wp4032/cs107e-final-project/math.c

#include "math.h"
#include "assert.h"
#include "printf.h"

void math_init(void) {
    return;
}

// Constant values of PI π
const float _pi = 3.141592653589793;
const float _pi_2 = 1.5707963267948966;
const float _pi_4 = 0.7853981633974483;

// Table of cos
// Domain is 0 degrees to 360 degrees
static float _cos[360] = {
    1.0,
    0.9998476951563913,
    0.9993908270190958,
    0.9986295347545738,
    0.9975640502598242,
    0.9961946980917455,
    0.9945218953682733,
    0.992546151641322,
    0.9902680687415704,
    0.9876883405951378,
    0.984807753012208,
    0.981627183447664,
    0.9781476007338057,
    0.9743700647852352,
    0.9702957262759965,
    0.9659258262890683,
    0.9612616959383189,
    0.9563047559630354,
    0.9510565162951535,
    0.9455185755993168,
    0.9396926207859084,
    0.9335804264972017,
    0.9271838545667874,
    0.9205048534524404,
    0.9135454576426009,
    0.9063077870366499,
    0.898794046299167,
    0.8910065241883679,
    0.882947592858927,
    0.8746197071393957,
    0.8660254037844387,
    0.8571673007021123,
    0.848048096156426,
    0.838670567945424,
    0.8290375725550416,
    0.8191520442889918,
    0.8090169943749475,
    0.7986355100472928,
    0.788010753606722,
    0.7771459614569709,
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
};

// Table of sin
// Domain is 0 degrees to 360 degrees
static float _sin[360] = {
    0.0,
    0.01745240643728351,
    0.03489949670250097,
    0.05233595624294383,
    0.0697564737441253,
    0.08715574274765817,
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

// FUNCTION: __cos
// PARAMS: int x
// RETURNS: cos(x) where x is the integer value of the degree
float __cos(int x) {
    return _cos[x % 360];
}

// FUNCTION: __cos
// PARAMS: int x
// RETURNS: sin(x) where x is the integer value of the degree
float __sin(int x) {
    return _sin[x % 360];
}

// FUNCTION: acos
// PARAMS: int x
// RETURNS: acos(x) where x 
float __acos(int x) {
    if (x < -100 || x > 100) {
        printf("acos(x = %d) is out of the domain of acos()", x);
        assert(0);
        return 0.0;
    }
    return _acos[x + 100];
}

// FUNCTION: asin
// PARAMS: int x
// RETURNS: sin(x) where x is the integer value of the degree
float __asin(int x) {
    if (x < -100 || x > 100) {
        printf("asin(x = %d) is out of the domain of sin()", x);
        assert(0);
        return 0.0;
    }
    return _asin[x + 100];
}

// FUNCTION: atan
// PARAMS: int x
// RETURNS: sin(x) where x is the integer value of the degree
float __atan(int x) {
    if (x > 1000) {
        return _pi_2;
    }
    if (x < -1000) {
        return -1 * _pi_2;
    }
    return _atan[x + 1000];
}


// TRIGONOMETRY FUNCTIONS
// Functions that can take in floats, but will be rounded and may be incorrect

float cos(float x) {
    return __cos((int) (x));
}

float sin(float x) {
    return __sin((int) (x));
}

float tan(float x) {
    return __sin((int) (x)) / __cos((int) (x));
}

float acos(float x) {
    return __acos((int) (x * 100));
}

float asin(float x) {
    return __asin((int) (x * 100));
}

float atan(float x) {
    return __atan((int) (x * 100));
}

float atan2(float y, float x) {
    return __atan((int) ((y / x) * 100));
}


// BASIC MATH FUNCTIONS
// Math functions that are very simple such as square root and power

// FUNCTION: pwr
// PARAMS: float a, signed int b
// RETURNS: a^b where a is a float and b is an integer
// CITATION: https://www.codeproject.com/Articles/570700/SquareplusRootplusalgorithmplusforplusC
float pwr(float a, signed int b) {
    float result = 1.0;
    if (b > 0) {
        for(int i = 0; i < b; i++) {
            result *= a;
        }
    }
    if (b < 0) {
        for(int i = 0; i < (0 - b); i++){
            result *= 1 / a;
        }
    }
    return result;
}

// FUNCTION: pwr10
// PARAMS: signed int b
// RETURNS: 10^b where b is an integer
// CITATION: https://www.codeproject.com/Articles/570700/SquareplusRootplusalgorithmplusforplusC
float pwr10(signed int b) {
    return pwr(10.0, b);
}

// FUNCTION: sqrt
// PARAMS: float a
// RETURNS: √ a where a is a float; returns 0 if given a negative value
// CITATION: https://www.codeproject.com/Articles/570700/SquareplusRootplusalgorithmplusforplusC
float sqrt(float a) {
    float temp = a;
    float result = 0.0;
    int max = 8;
    double j = 1.0;

    for(int i = max; i > 0; i--){
        if(temp - ((2 * result) + (j * pwr10(i))) * (j * pwr10(i)) >= 0) {
            while(temp - ((2 * result) + (j * pwr10(i)))*(j * pwr10(i)) >= 0) {
                j++;
                if(j >= 10) break;
            }
            j--;
            temp -= ((2 * result) + (j * pwr10(i)))*(j * pwr10(i));
            result += j * pwr10(i);
            j = 1.0;
        }
    }

    for (int i = 0; i >= 0 - max; i--) {
        if(temp - ((2 * result) + (j * pwr10(i))) * (j * pwr10(i)) >= 0) {
            while(temp - ((2 * result) + (j * pwr10(i)))*(j * pwr10(i)) >= 0) {
                j++;
            }
            j--;
            temp -= ((2 * result) + (j * pwr10(i))) * (j * pwr10(i));
            result += j * pwr10(i);
        }
    }

    return result;
}

// ABSTRACT / MODULUAR MATH FUNCTIONS
// Functions that deal with integers or miscellaneous 

// FUNCTION: floor
// PARAMS: float x
// RETURNS: the integer part of x
int floor(float x) {
    return (int) x;
}

// FUNCTION: round
// PARAMS: float x
// RETURNS: rounds x to the nearest integer
int round(float x) {
    return floor(x + 0.5);
}

// FUNCTION: decimals
// PARAMS: float x
// RETURNS: the decimal part of x
float decimals(float x) {
    return x - ((float) floor(x));
}

// FUNCTION: decimals_flipped
// PARAMS: float x
// RETURNS: the (1 - decimal part of x)
float decimals_flipped(float x) {
    return 1 - decimals(x);
}

// FUNCTION: swap
// PARAMS: int *a, int *b
// RETURNS: swaps the two integers
void swap(int *a, int *b) {
    int temp = *a;
    *a = *b;
    *b = temp;
}

// FUNCTION: abs
// PARAMS: signed int a
// RETURNS: the absolute value of a signed integer
unsigned int abs(signed int a) {
  if (a < 0) {
    return a * -1;
  }
  return a;
}


// VECTOR MATH
// Functions that deal with vectors
// Ended up not using but would be interested in further developing in the future

// FUNCTION: v_dot
// PARAMS: vector_t a, vector_t b
// RETURNS: vector dot product of a and b
float v_dot(vector_t a, vector_t b) {
  return (a.x * b.x) + (a.y * b.y) + (a.z + b.z);
}

// FUNCTION: v_add
// PARAMS: vector_t a, vector_t b
// RETURNS: vector addition of a and b
vector_t v_add(vector_t a, vector_t b) {
  vector_t result;
  result.x = a.x + b.x;
  result.y = a.y + b.y;
  result.z = a.z + b.z;
  return result;
}

// FUNCTION: v_sub
// PARAMS: vector_t a, vector_t b
// RETURNS: vector subtraction of a and b
vector_t v_sub(vector_t a, vector_t b) {
  vector_t result;
  result.x = a.x - b.x;
  result.y = a.y - b.y;
  result.z = a.z - b.z;
  return result;
}

// FUNCTION: v_multiply
// PARAMS: vector_t a, vector_t b
// RETURNS: vector and scalar multplication of a and b
vector_t v_multiply(vector_t a, float b) {
  vector_t result;
  result.x = a.x * b;
  result.y = a.y * b;
  result.z = a.z * b;
  return result;
}

// FUNCTION: v_multiply
// PARAMS: vector_t a, vector_t b
// RETURNS: vector and scalar division of a and b
vector_t v_divide(vector_t a, float b) {
  vector_t result;
  result.x = a.x / b;
  result.y = a.y / b;
  result.z = a.z / b;
  return result;
}
