wp4032/cs107e-final-project/title.c

#include "gl.h"
#include "settings.h"
#include "strings.h"
#include "timer.h"
#include "armtimer.h"

#define SPACING 5

typedef struct  {
    int img_width, img_height;
    unsigned int title_img[];
} title_image_t;

static const title_image_t title;


// FUNCTION: draw_title
// PARAMS: void
// RETURNS: draws the title screen for 5 seconds
void draw_title(void) {
  armtimer_disable_interrupts();
  int x_half = SCREEN_X / 2;
  int y_half = SCREEN_Y / 2;

  // Draws image of DREAMS DON'T DIE LOGO on screen
  for(int x = 0; x < title.img_width; x++) {
    for(int y = 0; y < title.img_height; y++) {
      color_t c = (color_t) (~title.title_img[x + (y * title.img_width)]);
      if (c != 0) {
        gl_draw_pixel(x + x_half - (title.img_width / 2), y + y_half - (title.img_height / 2), c);
      }
    }
  }

  int char_width = gl_get_char_width();
  int char_height = gl_get_char_height();

  const char *welcome = "Welcome to:";
  int wel_len = strlen(welcome) * char_width;
  const char *moonwalker = "M O O N W A L K E R   V 1 . 1";
  int moon_len = strlen(moonwalker) * char_width;
  const char *credit = "Copyright William Pan (williampan@stanford.edu) 2023";
  int cred_len = strlen(credit) * char_width;
  const char *allrights = "All Rights Reserved";
  int ar_len = strlen(allrights) * char_width;

  // Draws various other text (ones above)
  gl_draw_string(x_half - (wel_len / 2), y_half - (title.img_height / 2) - char_height - SPACING, welcome, GL_WHITE);
  gl_draw_string(x_half - (moon_len / 2), y_half + (title.img_height / 2) + char_height - 10, moonwalker, GL_WHITE);
  gl_draw_string(x_half - (cred_len / 2), y_half + (title.img_height / 2) + (2 * (char_height + SPACING)) + 20, credit, GL_WHITE);
  gl_draw_string(x_half - (ar_len / 2), y_half + (title.img_height / 2) + (3 * (char_height + SPACING)) + 20, allrights, GL_WHITE);

  gl_swap_buffer();

  timer_delay(5);
  armtimer_enable_interrupts();
}


// title_image_t holds the color values of the image
static const title_image_t title = {
  .img_width = 249,
  .img_height = 124,
  .title_img = {
    0xffffffff,	0xffffffff,	0xffffffff,	0xffffffff,	0xffffffff,	0xffffffff,	0xffffffff,	0xffffffff,	0xffffffff,	0xffffffff,	0xffffffff,	0xffffffff,	0xffffffff,	0xffffffff,	0xffffffff,	0xffffffff,	0xffffffff,	0xffffffff,	0xffffffff,	0xffffffff,	0xffffffff,	0xffffffff,	0xffffffff,	0xffffffff,	0xffffffff,	0xffffffff,	0xffffffff,	0xffffffff,	0xffffffff,	0xffffffff,	0xffffffff,	0xffffffff,	0xffffffff,	0xffffffff,	0xffffffff,	0xffffffff,	0xffffffff,	0xffffffff,	0xffffffff,	0xffffffff,	0xffffffff,	0xffffffff,	0xffffffff,	0xffffffff,	0xffffffff,	0xffffffff,	0xffffffff,	0xffffffff,	0xffffffff,	0xffffffff,	
    0xffffffff,	0xffffffff,	0xffffffff,	0xffffffff,	0xffffffff,	0xffffffff,	0xffffffff,	0xffffffff,	0xffffffff,	0xffffffff,	0xffffffff,	0xffffffff,	0xffffffff,	0xffffffff,	0xffffffff,	0xffffffff,	0xffffffff,	0xffffffff,	0xffffffff,	0xffffffff,	0xffffffff,	0xffffffff,	0xffffffff,	0xffffffff,	0xffffffff,	0xffffffff,	0xffffffff,	0xffffffff,	0xffffffff,	0xffffffff,	0xffffffff,	0xffffffff,	0xffffffff,	0xffffffff,	0xffffffff,	0xffffffff,	0xffffffff,	0xffffffff,	0xffffffff,	0xffffffff,	0xffffffff,	0xffffffff,	0xffffffff,	0xffffffff,	0xffffffff,	0xffffffff,	0xffffffff,	0xffffffff,	0xffffffff,	0xffffffff,	
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
  },
};
