wp4032/cs107e-final-project/gl.h

#ifndef GL_H
#define GL_H

/*
 * Functions for a simple bare metal Raspberry Pi graphics library
 * that draws pixels, text, lines, triangles, and rectangles. Builds
 * on the lower-level framebuffer library fb.[ch] for framebuffer
 * access and configuration; trying to use both fb and gl
 * simultaneously is discouraged.
 *
 * Students implement this module in assignment 6 (text and rectangles
 * are required, lines and triangles are an extension).
 * 
 * Additional functions added by William Pan <williampan@stanford.edu>
 *
 * Author: Philip Levis <pal@cs.stanford.edu>
 * Date: Mar 23 2016
 */

#include "fb.h"

typedef enum { GL_SINGLEBUFFER = FB_SINGLEBUFFER, GL_DOUBLEBUFFER = FB_DOUBLEBUFFER } gl_mode_t;

/*
 * `gl_init` : Required initialized for graphics library
 *
 * Initialize the graphic library. This function will call `fb_init` in turn
 * to initialize the framebuffer. The framebuffer will be initialzed to
 * 4-byte depth (32 bits per pixel).
 *
 * @param width  the requested width in pixels of the framebuffer
 * @param height the requested height in pixels of the framebuffer
 * @param mode   whether the framebuffer should be
 *                  single buffered (GL_SINGLEBUFFER)
 *                  or double buffered (GL_DOUBLEBUFFER)
 */
void gl_init(unsigned int width, unsigned int height, gl_mode_t mode);

/*
 * `gl_get_width`
 *
 * Get the current width in pixels of the framebuffer.
 *
 * @return    the width in pixels
 */
unsigned int gl_get_width(void);

/*
 * `gl_get_height`
 *
 * Get the current height in pixels of the framebuffer.
 *
 * @return    the height in pixels
 */
unsigned int gl_get_height(void);

/*
 * `color_t`
 *
 * Define a type for color. We use BGRA colors, where each color
 * component R, B, G, or A is a single unsigned byte. The least
 * signficant byte is the B component, and A is most significant.
 */
typedef unsigned int color_t;

/*
 * Define some common colors ...
 *
 * Note that colors are BGRA, where B is the first byte in memory
 * and the least significant byte in the unsigned word.
 */
#define GL_BLACK    0xFF000000
#define GL_WHITE    0xFFFFFFFF
#define GL_RED      0xFFFF0000
#define GL_GREEN    0xFF00FF00
#define GL_BLUE     0xFF0000FF
#define GL_CYAN     0xFF00FFFF
#define GL_MAGENTA  0xFFFF00FF
#define GL_YELLOW   0xFFFFFF00
#define GL_AMBER    0xFFFFBF00
#define GL_ORANGE   0xFFFF3F00
#define GL_PURPLE   0xFF7F00FF
#define GL_INDIGO   0xFF000040
#define GL_CAYENNE  0xFF400000
#define GL_MOSS     0xFF004000
#define GL_SILVER   0xFFBBBBBB

/*
 * `gl_color`
*
 * Returns a color composed of the specified red, green, and
 * blue components. The alpha component of the color will be
 * set to 0xff (fully opaque).
 *
 * @param r  the red component of the color
 * @param g  the green component of the color
 * @param b  the blue component of the color
 *
 * @return   the color as a single value of type color_t
 */
color_t gl_color(unsigned char r, unsigned char g, unsigned char b);

/*
 * `gl_clear`
 *
 * Clear all the pixels in the framebuffer to the given color.
 *
 * @param c  the color drawn into the framebuffer
 */
void gl_clear(color_t c);

/*
 * `gl_swap_buffer`
 *
 * If in double-buffered mode, all gl drawing takes place in the
 * off-screen buffer and updated drawing is not brought on-screen until
 * a call is made to `gl_swap_buffer` to exchange the on-screen
 * and off-screen buffers.
 *
 * If not in double-buffer mode, all drawing takes place on-screen and
 * the `gl_swap_buffer` function has no effect.
 */
void gl_swap_buffer(void);

/*
 * `gl_draw_pixel`
 *
 * Draw a single pixel at location x,y in color c.
 * If the location is outside the bounds of framebuffer, it is not drawn.
 *
 * @param x  the x location of the pixel
 * @param y  the y location of the pixel
 * @param c  the color of the pixel
 */
void gl_draw_pixel(int x, int y, color_t c);

/*
 * `gl_read_pixel`
 *
 * Return the color of the pixel at location x,y. Returns 0 if the
 * location is outside the bounds of the framebuffer.
 *
 * @param x  the x location of the pixel
 * @param y  the y location of the pixel
 *
 * @return   the color at that location
 */
color_t gl_read_pixel(int x, int y);

/*
 * `gl_draw_char`
 *
 * Draw a single character at location x,y in color c.
 * Only those pixels of the character that lie within the bounds
 * of the framebuffer are drawn. Any pixel that lies outside is
 * clipped (i.e. not drawn). Only the "on" pixels of the character
 * are drawn, all "off" pixels are left as-is.
 *
 * @param x   the x location of the upper left corner of the character glyph
 * @param y   the y location of the upper left corner of the character glyph
 * @param ch  the character to be drawn, e.g. 'a'. If this character has no glyph
 *            in the current font, nothing is drawn (refer to font_get_glyph())
 * @param c   the color of the character
 */
void gl_draw_char(int x, int y, char ch, color_t c);

/*
 * `gl_draw_string`
 *
 * Draw a string at location x,y in color c. The characters are drawn
 * left to right in a single line. Only the pixels of the characters
 * that lie within the bounds of the framebuffer are drawn. Any pixel
 * that lies outside is clipped (i.e. not drawn). Only the "on" pixels of
 * the characters are drawn, all "off" pixels are left as-is.
 *
 * @param x    the x location of the upper left corner of the first char of string
 * @param y    the y location of the upper left corner of the first char of string
 * @param str  the null-terminated string to be drawn
 * @param c    the color of the string
 */
void gl_draw_string(int x, int y, const char* str, color_t c);
void gl_draw_string_center(const char* str, color_t c);

/*
 * `gl_get_char_height`
 *
 * Get the height in pixels of a single character glyph.
 *
 * @return the height of character glyph in pixels
 */
unsigned int gl_get_char_height(void);

/*
 * `gl_get_char_width`
 *
 * Get the width in pixels of a single character glyph.
 *
 * @return the width of character glyph in pixels
 */
unsigned int gl_get_char_width(void);

/*
 * `gl_draw_rect`
 *
 * Draw a filled rectangle at location x,y with size w,h filled with color c.
 * All pixels in the rectangle that lie within the bounds of the
 * framebuffer are drawn. Any pixel that lies outside is clipped (i.e. not drawn).
 *
 * @param x  the x location of the upper left corner of the rectangle
 * @param y  the y location of the upper left corner of the rectangle
 * @param w  the width of the rectangle
 * @param h  the height of the rectangle
 * @param c  the color of the rectangle
 */
void gl_draw_rect(int x, int y, int w, int h, color_t c);

/*
 * `gl_draw_line`: optional extension
 *
 * Draw a line segment from location x1,y1 to location x2,y2 of color c.
 * All pixels along the line that lie within the bounds of the framebuffer
 * are drawn. Any pixel that lies outside is clipped (i.e. not drawn).
 *
 * @param x1  the x location of vertex 1
 * @param y1  the y location of vertex 1
 * @param x2  the x location of vertex 2
 * @param y2  the y location of vertex 2
 * @param c   the color of the line
 *
 * This function is NOT part of the core requirements.
 * You can leave this function unimplemented if not doing the extension.
 */
void gl_draw_line(int x1, int y1, int x2, int y2, color_t c);

/*
 * `gl_draw_triangle`: optional extension
 *
 * Draw a filled triangle connecting the three vertices filled with color c.
 * All pixels within the triangle that lie within the bounds of the
 * framebuffer are drawn. Any pixel that lies outside is clipped (i.e. not drawn).
 *
 * @param x1  the x location of vertex 1
 * @param y1  the y location of vertex 1
 * @param x2  the x location of vertex 2
 * @param y2  the y location of vertex 2
 * @param x3  the x location of vertex 3
 * @param y3  the y location of vertex 3
 * @param c   the color of the triangle
 *
 * This function is NOT part of the core requirements.
 * You can leave this function unimplemented if not doing the extension.
 */
void gl_draw_triangle(int x1, int y1, int x2, int y2, int x3, int y3, color_t c);

void gl_copy_buffer(void);

void gl_draw_circle_outline(int x, int y, int r, color_t c);
void gl_draw_circle_filled(int x, int y, int r, color_t c);
void gl_draw_circle_octant(int x, int y, int center_x, int center_y, color_t c);
void gl_draw_circle_octant_filled(int x, int y, int center_x, int center_y, color_t c);

#endif
