wp4032/cs107e-final-project/messages.c

#include "printf.h"
#include "gl.h"
#include "settings.h"
#include "timer.h"
#include "messages.h"
#include "accel.h" // delete after
#include "armtimer.h"

color_t back = GL_BLUE;
color_t front = GL_WHITE;

static void draw_flash(const char *str, color_t front, color_t back, int delay);

static const char *strings[5] = {
  "center",
  "top left",
  "top right",
  "bottom left",
  "bottom right",
};


// PRINT FUNCTIONS
// Functions that print into terminal

void print_title(void) {
  printf("Welcome to:\n Dreams Don't Die - Moonwalker\nby: William Pan (williampan@stanford.edu)\nMarch 28, 2023\n");
}

void print_start_calibration(void) {
  print_calibration_message(SCREEN_X / 2, SCREEN_Y / 2, 15, 0);             // Point to center
  print_calibration_message(15, 15, 15, 1);                                 // Point to top left
  print_calibration_message(SCREEN_X - 15, 15, 15, 2);                      // Point to top right
  print_calibration_message(15, SCREEN_Y - 15, 15, 3);                      // Point to bottom left
  print_calibration_message(SCREEN_X - 15, SCREEN_Y - 15, 15, 4);           // Point to bottom right
}

void print_calibration_message(int x, int y, int r, int i) {
  printf("\nStarting calibration [%d / 5]...\nPoint your arm at the %s...\n", i + 1, strings[i]);
  gl_draw_circle_filled(x, y, r, GL_WHITE);
  gl_copy_buffer();
  timer_delay(1);
  printf("\n[3]");
  timer_delay(1);
  printf("\n[2]");
  timer_delay(1);
  printf("\n[1]\n");
  accel_print_angles();
}

void print_calibration_try_again(void) {
  printf("\nRestarting calibration again...\nTry to point your arm straight toward the screen\n");
  timer_delay(1);
  printf("\n[3]");
  timer_delay(1);
  printf("\n[2]");
  timer_delay(1);
  printf("\n[1]\n");
}

void print_calibration_success(void) {
  printf("\n\nCalibration successful!\n");
}

void print_calibration_failure(void) {
  printf("\n\nCalibration failed!\n");
}

void print_error(void) {
  printf("\n\nError occured! Restart the device :(\n");
}


// DRAW FUNCTIONS
// Functions that draw onto the screen

void draw_start_calibration(void) {
  draw_calibration_message(SCREEN_X / 2, SCREEN_Y / 2, 15, 0);             // Point to center
  draw_calibration_message(15, 15, 15, 1);                                 // Point to top left
  draw_calibration_message(SCREEN_X - 15, 15, 15, 2);                      // Point to top right
  draw_calibration_message(15, SCREEN_Y - 15, 15, 3);                      // Point to bottom left
  draw_calibration_message(SCREEN_X - 15, SCREEN_Y - 15, 15, 4);           // Point to bottom right
}

void draw_calibration_message(int x, int y, int r, int i) {
  char buf[1024];
  snprintf(buf, 1024, "Starting calibration [%d / 5]", i + 1);
  gl_draw_string_center(buf, GL_WHITE);
  gl_copy_buffer();
  timer_delay(1);
  gl_draw_string_center(buf, GL_BLUE);
  gl_copy_buffer();

  snprintf(buf, 1024, "Point your arm at the %s", strings[i]);
  gl_draw_string_center(buf, GL_WHITE);
  gl_copy_buffer();
  timer_delay(1);
  gl_draw_string_center(buf, GL_BLUE);
  gl_copy_buffer();
  
  gl_draw_circle_filled(x, y, r, GL_WHITE);
  gl_copy_buffer();

  if (i == 0) {
    draw_flash("3", GL_BLUE, GL_WHITE, 1);
    draw_flash("2", GL_BLUE, GL_WHITE, 1);
    draw_flash("1", GL_BLUE, GL_WHITE, 1);
  }

  else {
    draw_flash("3", front, back, 1);
    draw_flash("2", front, back, 1);
    draw_flash("1", front, back, 1);
  }

  gl_draw_circle_filled(x, y, r, GL_BLUE);
}

void draw_calibration_success(void) {
  draw_flash("Calibration success!", front, back, 1);
}

void draw_calibration_failure(void) {
  draw_flash("Calibration failed!", front, back, 1);
}

void draw_calibration_try_again(void) {
  draw_flash("Restarting calibration again...", front, back, 1);
  draw_flash("3", front, back, 1);
  draw_flash("2", front, back, 1);
  draw_flash("1", front, back, 1);
}

void draw_error(void) {
    draw_flash("Error occured! Restart the device :(", front, back, 1);
}

static void draw_flash(const char *str, color_t front, color_t back, int delay) {
  armtimer_disable_interrupts();
  gl_draw_string_center(str, front);
  gl_copy_buffer();
  timer_delay(delay);
  gl_draw_string_center(str, back);
  gl_copy_buffer();
  armtimer_enable_interrupts();
}
